DinoLeung/can-bus-injector/include/gps_snapshot.h

#pragma once

#include <stdint.h>
#include <TinyGPSPlus.h>

struct GpsSnapshot {
	bool timeValid;
	uint8_t hour;
	uint8_t minute;
	uint8_t second;
	uint16_t milliseconds;

	bool dateValid;
	uint16_t year;
	uint8_t month;
	uint8_t day;

	bool locationValid;
	double latitudeDeg;
	double longitudeDeg;
	TinyGPSLocation::Quality fixQuality;

	bool altitudeValid;
	double altitudeMeters;

	bool speedValid;
	double speedKmh;

	bool courseValid;
	double courseDeg;

	bool satellitesValid;
	uint32_t satellites;

	bool hdopValid;
	float hdop;

	bool vdopValid;
	float vdop;
};

void initGpsSnapshot();
void updateGpsSnapshot();
void getGpsSnapshot(GpsSnapshot& out);
